svenpetersen1965/C64-WiFi-Modem-User-Port/Case/for PCB Rev. 1/label/inkscape/C64-Wifi_UserP v34.png

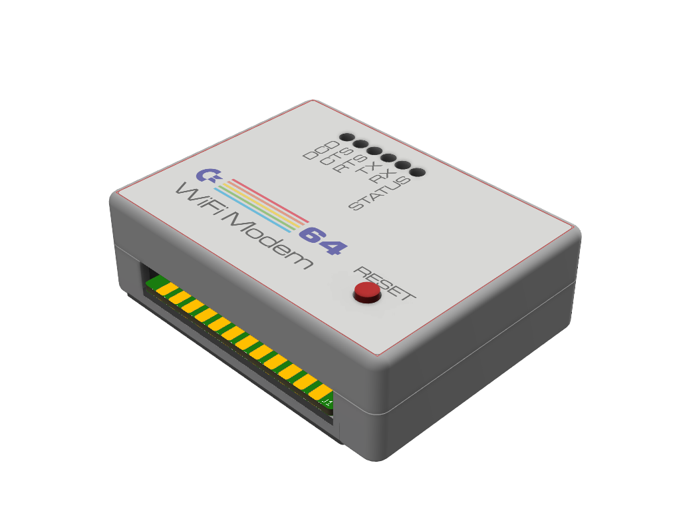
Case/for PCB Rev. 1/label/inkscape/C64-Wifi_UserP v34.png
