svenpetersen1965/C64-WiFi-Modem-User-Port/Case/for PCB Rev. 1/label/inkscape/WiFi_Modem_label.png

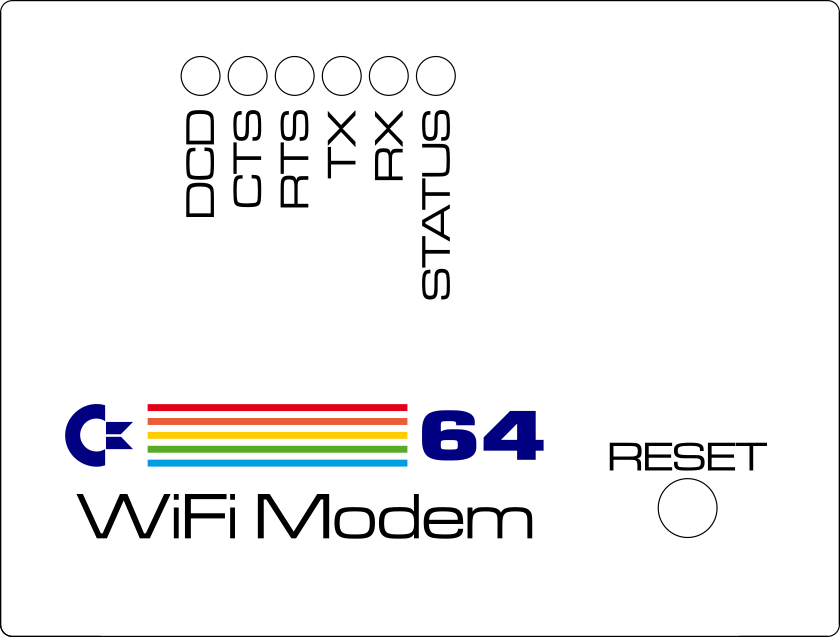
Case/for PCB Rev. 1/label/inkscape/WiFi_Modem_label.png
