svenpetersen1965/C64-WiFi-Modem-User-Port/Case/for PCB Rev. 2/label/inkscape/label_flipped.png

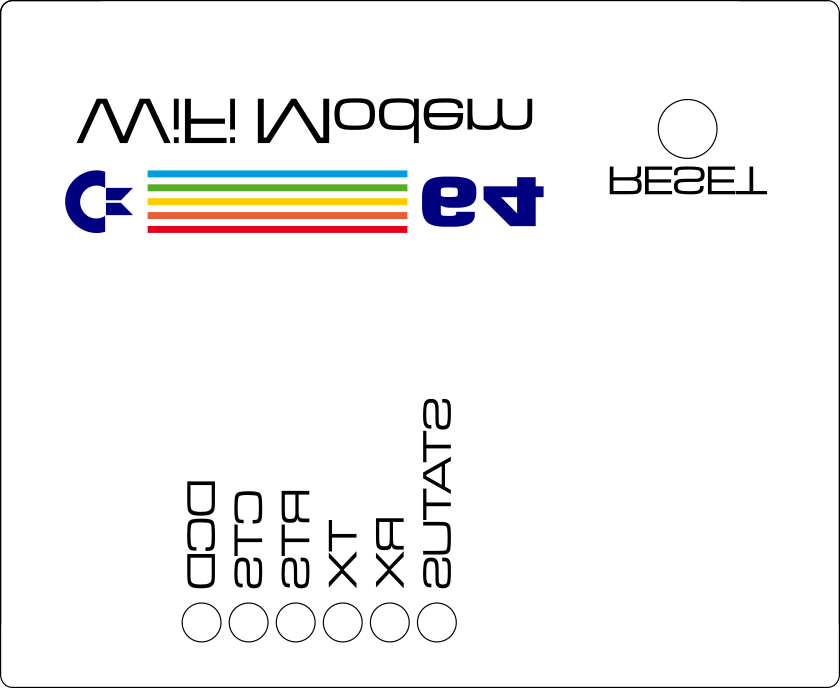
Case/for PCB Rev. 2/label/inkscape/label_flipped.png
